simonantonio/Wireless-Sensor/Source/Configuration.h

/*
	User configurable items
*/

#ifndef _CONFIGURATION_H_
#define _CONFIGURATION_H_

#define ALTITUDE 40.0 // Altitude of Home Location (meters)

#define IS_WEATHER_SENSOR true 

//Used for Pulse 2 detection [Digital 9]
//but we will use it to flash a LED if their is an error
#define ERROR_PIN 9 

#endif //_CONFIGURATION_H_
